rubini/thub-0/sw/include/string.h

extern char *strcpy(char * d, char *s);
extern int strlen(char *s);
extern int strnlen(char *s, int count);
extern void *memcpy(void *d, void *s, int count);
extern void *memset(void *d, int c, int count);
